kidmd/WDW-costumes/3d_panels/active_artwork.png

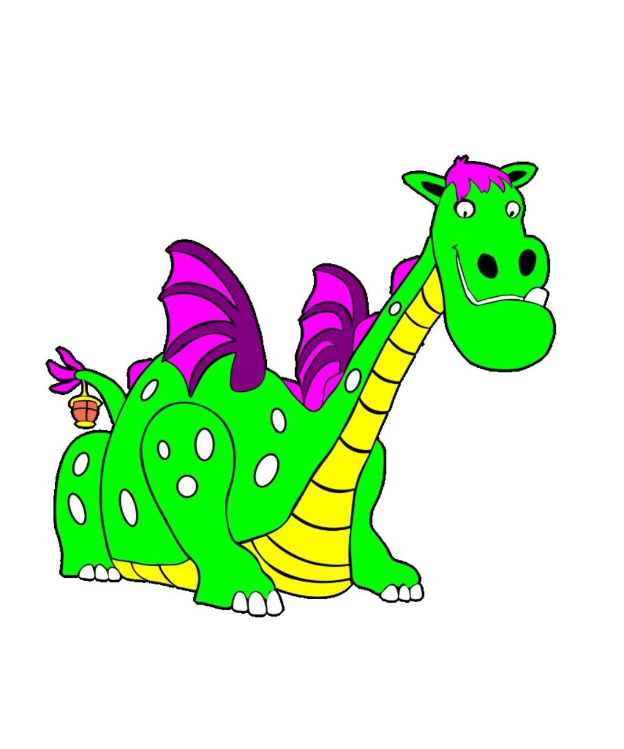
3d_panels/active_artwork.png
