kidmd/WDW-costumes/assets/petes_dragon.png

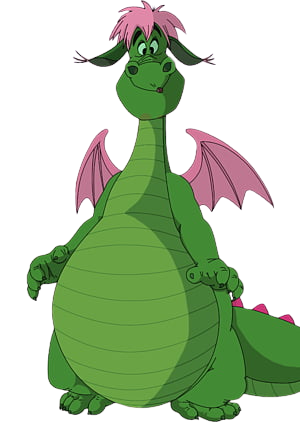
assets/petes_dragon.png
