kidmd/WDW-costumes/assets/snail2_raw_upload.png

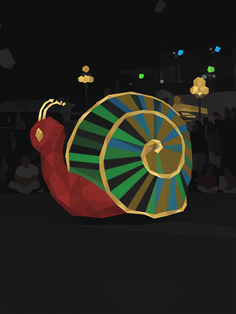
assets/snail2_raw_upload.png
