kidmd/WDW-costumes/assets/spinning_turtle.png

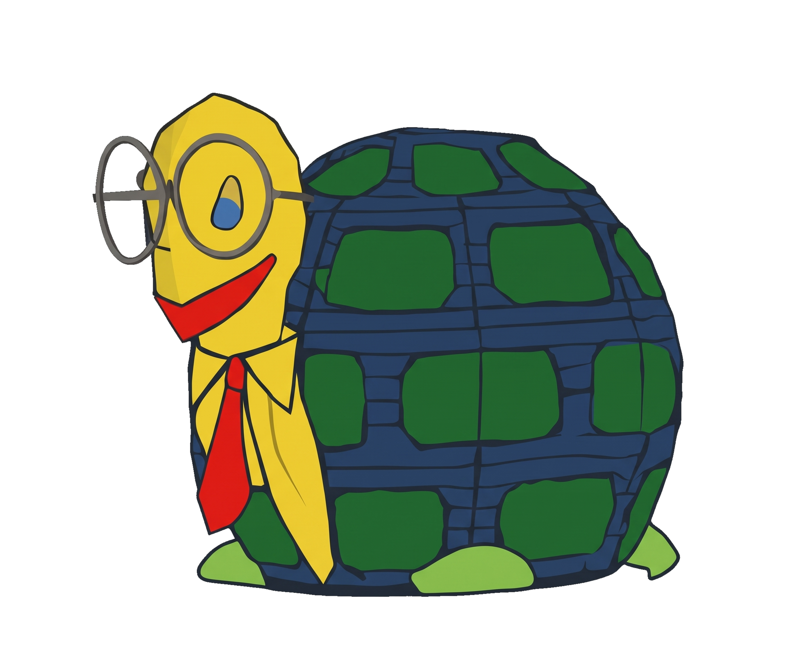
assets/spinning_turtle.png
