kidmd/WDW-costumes/assets/title_drum.png

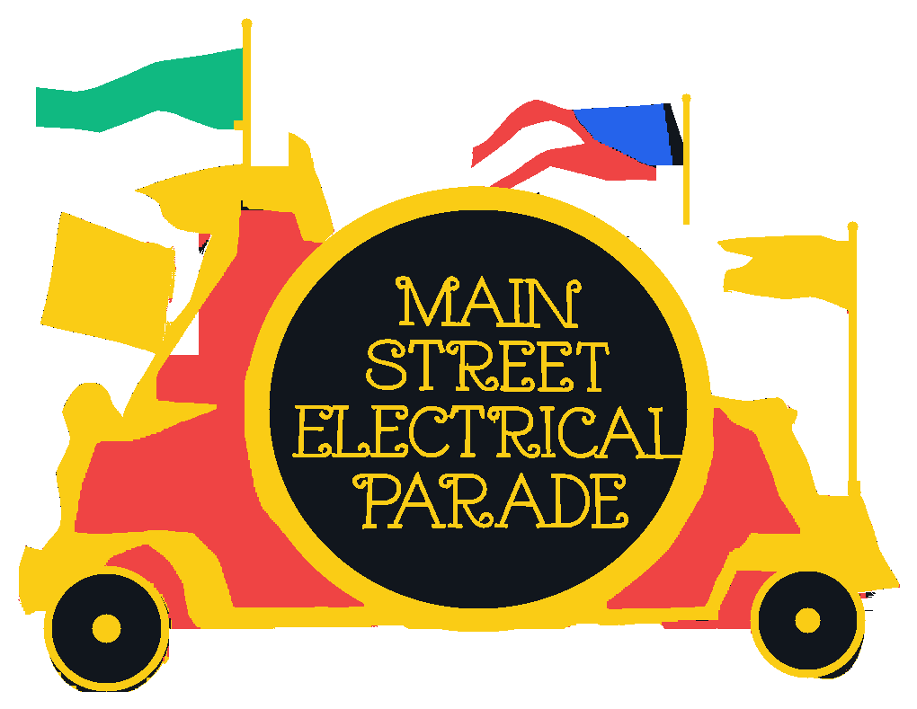
assets/title_drum.png
