kidmd/WDW-costumes/assets/Turtle_clean.jpg

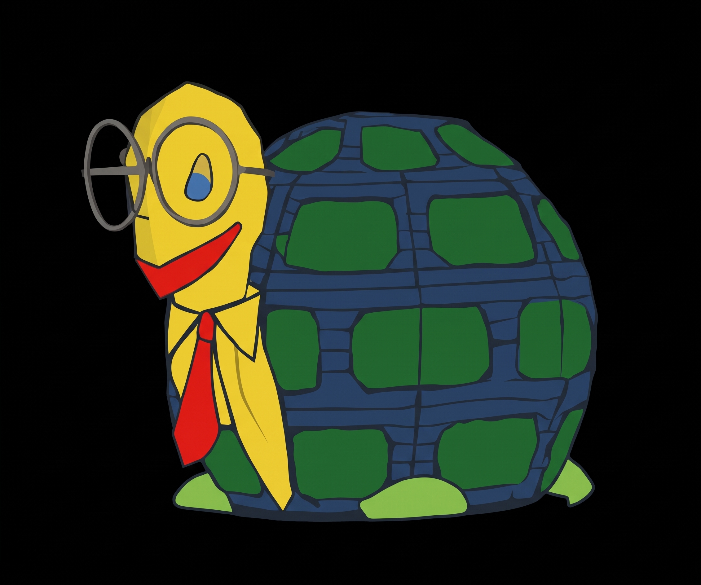
assets/Turtle_clean.jpg
