kidmd/WDW-costumes/simulator/assets/Snail.png

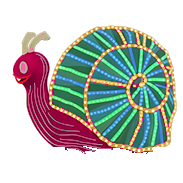
simulator/assets/Snail.png
