kidmd/WDW-costumes/simulator/assets/Turtle.png

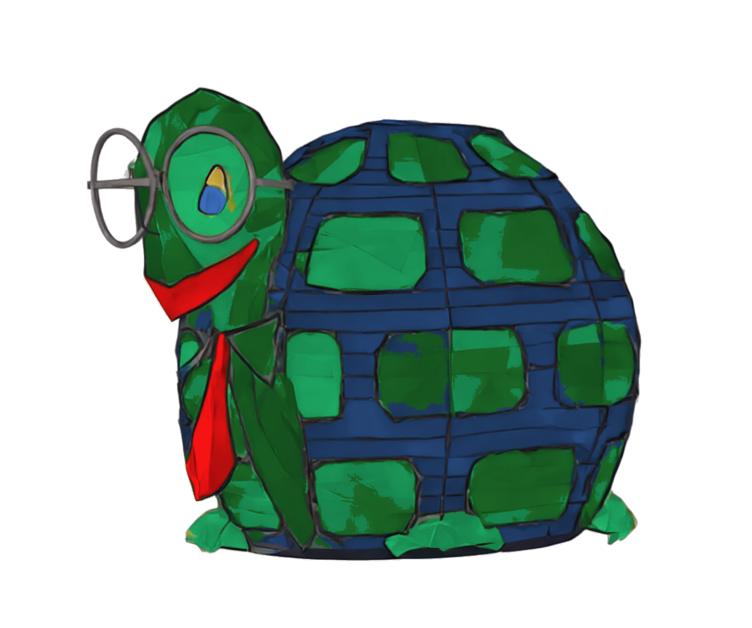
simulator/assets/Turtle.png
