kidmd/WDW-costumes/arduino/MSEP_Costume/fleet_palettes.h

#ifndef FLEET_PALETTES_H
#define FLEET_PALETTES_H

#include <FastLED.h>

#define HAS_DEFAULT_FLOAT_PALETTES 1

// Authentic default background graphic colors for all 7 floats (100 LEDs each)
// Used for 📸 Castle Photo Mode and default float palettes
const CRGB PROGMEM DEFAULT_FLOAT_PALETTES[7][100] = {
    // Float 1: The Train (Casey Jr.)
    {
        CRGB(255, 183, 3),
        CRGB(255, 183, 3),
        CRGB(255, 183, 3),
        CRGB(255, 183, 3),
        CRGB(255, 183, 3),
        CRGB(255, 183, 3),
        CRGB(255, 183, 3),
        CRGB(255, 183, 3),
        CRGB(255, 183, 3),
        CRGB(255, 183, 3),
        CRGB(255, 183, 3),
        CRGB(255, 183, 3),
        CRGB(255, 183, 3),
        CRGB(255, 183, 3),
        CRGB(255, 183, 3),
        CRGB(255, 183, 3),
        CRGB(255, 183, 3),
        CRGB(255, 183, 3),
        CRGB(255, 183, 3),
        CRGB(255, 183, 3),
        CRGB(255, 183, 3),
        CRGB(255, 183, 3),
        CRGB(255, 183, 3),
        CRGB(255, 183, 3),
        CRGB(255, 183, 3),
        CRGB(255, 183, 3),
        CRGB(255, 183, 3),
        CRGB(255, 183, 3),
        CRGB(230, 57, 70),
        CRGB(230, 57, 70),
        CRGB(230, 57, 70),
        CRGB(230, 57, 70),
        CRGB(230, 57, 70),
        CRGB(230, 57, 70),
        CRGB(230, 57, 70),
        CRGB(230, 57, 70),
        CRGB(230, 57, 70),
        CRGB(230, 57, 70),
        CRGB(230, 57, 70),
        CRGB(230, 57, 70),
        CRGB(230, 57, 70),
        CRGB(230, 57, 70),
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
        CRGB(40, 90, 240),
        CRGB(40, 90, 240),
        CRGB(40, 90, 240),
        CRGB(230, 40, 40),
        CRGB(230, 40, 40),
        CRGB(230, 40, 40),
        CRGB(230, 40, 40),
        CRGB(230, 40, 40),
        CRGB(230, 40, 40)
    }
};

#endif // FLEET_PALETTES_H
