kidmd/WDW-costumes/simulator.py

#!/usr/bin/env python3
"""
Main Street Electrical Parade - LED Costume Simulator & Visualizer
Serves the interactive web interface locally and manages costume preset files.
"""

import http.server
import socketserver
import os
import sys
import json
import webbrowser
import threading
import urllib.parse
import socket
import re
import subprocess
import time
import math

# UDP Pixel Streaming Socket
udp_socket = socket.socket(socket.AF_INET, socket.SOCK_DGRAM)
try:
    udp_socket.setsockopt(socket.SOL_SOCKET, socket.SO_BROADCAST, 1)
except Exception as e:
    print(f"[WARN] Could not enable SO_BROADCAST on UDP socket: {e}")
UDP_STREAM_PORT = 4210

DEFAULT_PORT = 8000
BASE_DIR = os.path.dirname(os.path.abspath(__file__))
SIMULATOR_DIR = os.path.join(BASE_DIR, "simulator")
PRESETS_DIR = os.path.join(BASE_DIR, "presets")
FLEET_SHOWS_DIR = os.path.join(PRESETS_DIR, "fleet_shows")

# Ensure presets and fleet_shows directories exist
os.makedirs(PRESETS_DIR, exist_ok=True)
os.makedirs(FLEET_SHOWS_DIR, exist_ok=True)

class SimulatorRequestHandler(http.server.SimpleHTTPRequestHandler):
    def __init__(self, *args, **kwargs):
        super().__init__(*args, directory=SIMULATOR_DIR, **kwargs)

    def log_message(self, format, *args):
        # Keep console output concise
        pass

    def end_headers(self):
        self.send_header("Cache-Control", "no-store, no-cache, must-revalidate, max-age=0")
        self.send_header("Pragma", "no-cache")
        self.send_header("Expires", "0")
        super().end_headers()

    def do_GET(self):
        parsed = urllib.parse.urlparse(self.path)
        if parsed.path == "/api/presets":
            self.handle_list_presets()
        elif parsed.path == "/api/serial_status":
            self.handle_serial_status()
        elif parsed.path == "/api/wifi_config":
            self.handle_get_wifi_config()
        elif parsed.path == "/api/fleet_config":
            self.handle_get_fleet_config()
        elif parsed.path == "/api/fleet_shows":
            self.handle_list_fleet_shows()
        elif parsed.path == "/api/fleet_radar":
            self.handle_get_fleet_radar()
        elif parsed.path == "/api/build_fleet_binaries":
            self.handle_build_fleet_binaries()
        elif parsed.path == "/api/generate_tpu_stl":
            self.handle_generate_tpu_stl()
        elif parsed.path.startswith("/api/fleet_show/"):
            filename = urllib.parse.unquote(parsed.path[len("/api/fleet_show/"):])
            self.handle_get_fleet_show(filename)
        elif parsed.path.startswith("/api/preset/"):
            filename = urllib.parse.unquote(parsed.path[len("/api/preset/"):])
            self.handle_get_preset(filename)
        elif parsed.path.startswith("/firmware/"):
            rel_path = parsed.path[len("/firmware/"):]
            firmware_file = os.path.join(BASE_DIR, "firmware", rel_path)
            if os.path.exists(firmware_file) and os.path.isfile(firmware_file):
                self.send_response(200)
                if firmware_file.endswith(".bin"):
                    self.send_header("Content-Type", "application/octet-stream")
                elif firmware_file.endswith(".json"):
                    self.send_header("Content-Type", "application/json")
                else:
                    self.send_header("Content-Type", "text/plain")
                self.send_header("Content-Length", str(os.path.getsize(firmware_file)))
                self.send_header("Access-Control-Allow-Origin", "*")
                self.end_headers()
                with open(firmware_file, "rb") as f:
                    self.wfile.write(f.read())
                return
            else:
                self.send_error(404, "Firmware file not found")
                return
        elif parsed.path == "/SIMULATOR_USER_GUIDE.md":
            guide_path = os.path.join(BASE_DIR, "SIMULATOR_USER_GUIDE.md")
            if os.path.exists(guide_path):
                self.send_response(200)
                self.send_header("Content-Type", "text/markdown; charset=utf-8")
                self.send_header("Content-Length", str(os.path.getsize(guide_path)))
                self.end_headers()
                with open(guide_path, "rb") as f:
                    self.wfile.write(f.read())
                return
            else:
                self.send_error(404, "Guide not found")
                return
        elif parsed.path.startswith("/assets/"):
            rel_asset = urllib.parse.unquote(parsed.path[len("/assets/"):])
            # Check simulator/assets first, then root assets
            asset_path = os.path.join(SIMULATOR_DIR, "assets", rel_asset)
            if not os.path.exists(asset_path):
                asset_path = os.path.join(BASE_DIR, "assets", rel_asset)
            if os.path.exists(asset_path) and os.path.isfile(asset_path):
                self.send_response(200)
                if asset_path.endswith(".png"):
                    self.send_header("Content-Type", "image/png")
                elif asset_path.endswith(".jpg") or asset_path.endswith(".jpeg"):
                    self.send_header("Content-Type", "image/jpeg")
                elif asset_path.endswith(".svg"):
                    self.send_header("Content-Type", "image/svg+xml")
                else:
                    self.send_header("Content-Type", "application/octet-stream")
                self.send_header("Content-Length", str(os.path.getsize(asset_path)))
                self.send_header("Access-Control-Allow-Origin", "*")
                self.end_headers()
                with open(asset_path, "rb") as f:
                    self.wfile.write(f.read())
                return
            else:
                self.send_error(404, "Asset file not found")
                return
        elif parsed.path.startswith("/pcb/"):
            rel_pcb = urllib.parse.unquote(parsed.path[len("/pcb/"):])
            if not rel_pcb or rel_pcb == "/":
                rel_pcb = "pcb_preview.html"
            pcb_file = os.path.join(BASE_DIR, "pcb", rel_pcb)
            if os.path.exists(pcb_file) and os.path.isfile(pcb_file):
                self.send_response(200)
                if pcb_file.endswith(".html"):
                    self.send_header("Content-Type", "text/html; charset=utf-8")
                elif pcb_file.endswith(".csv"):
                    self.send_header("Content-Type", "text/csv; charset=utf-8")
                elif pcb_file.endswith(".kicad_pcb"):
                    self.send_header("Content-Type", "text/plain; charset=utf-8")
                else:
                    self.send_header("Content-Type", "application/octet-stream")
                self.send_header("Content-Length", str(os.path.getsize(pcb_file)))
                self.send_header("Access-Control-Allow-Origin", "*")
                self.end_headers()
                with open(pcb_file, "rb") as f:
                    self.wfile.write(f.read())
                return
            else:
                self.send_error(404, "PCB file not found")
                return
        elif parsed.path.startswith("/3d_panels/"):
            rel_panel = urllib.parse.unquote(parsed.path[len("/3d_panels/"):])
            if not rel_panel or rel_panel == "/":
                rel_panel = "tpu_panel_preview.html"
            panel_file = os.path.join(BASE_DIR, "3d_panels", rel_panel)
            if os.path.exists(panel_file) and os.path.isfile(panel_file):
                self.send_response(200)
                if panel_file.endswith(".html"):
                    self.send_header("Content-Type", "text/html; charset=utf-8")
                elif panel_file.endswith(".json"):
                    self.send_header("Content-Type", "application/json; charset=utf-8")
                elif panel_file.endswith(".3mf"):
                    self.send_header("Content-Type", "model/3mf")
                elif panel_file.endswith(".zip"):
                    self.send_header("Content-Type", "application/zip")
                elif panel_file.endswith(".stl"):
                    self.send_header("Content-Type", "model/stl")
                elif panel_file.endswith(".scad"):
                    self.send_header("Content-Type", "application/octet-stream")
                else:
                    self.send_header("Content-Type", "application/octet-stream")
                self.send_header("Content-Length", str(os.path.getsize(panel_file)))
                self.send_header("Access-Control-Allow-Origin", "*")
                self.send_header("Cache-Control", "no-cache, no-store, must-revalidate")
                self.send_header("Pragma", "no-cache")
                self.send_header("Expires", "0")
                self.end_headers()
                with open(panel_file, "rb") as f:
                    self.wfile.write(f.read())
                return
            else:
                self.send_error(404, "3D Panel file not found")
                return
        else:
            super().do_GET()

    def do_POST(self):
        parsed = urllib.parse.urlparse(self.path)
        if parsed.path == "/api/save_preset":
            self.handle_save_preset()
        elif parsed.path == "/api/save_fleet_config":
            self.handle_save_fleet_config()
        elif parsed.path == "/api/save_fleet_show":
            self.handle_save_fleet_show()
        elif parsed.path == "/api/flash_firmware":
            self.handle_flash_firmware()
        elif parsed.path == "/api/stream_pixels":
            self.handle_stream_pixels()
        elif parsed.path == "/api/save_wifi":
            self.handle_save_wifi()
        elif parsed.path == "/api/flash_wifi_receiver":
            self.handle_flash_wifi_receiver()
        elif parsed.path == "/api/export_fleet_routine":
            self.handle_export_fleet_routine()
        elif parsed.path == "/api/build_fleet_binaries":
            self.handle_build_fleet_binaries()
        elif parsed.path == "/api/fleet_radar/scan":
            self.handle_fleet_radar_scan()
        elif parsed.path == "/api/fleet_radar/identify":
            self.handle_fleet_radar_identify()
        elif parsed.path == "/api/fleet_radar/trigger_roll_call":
            self.handle_fleet_radar_trigger_roll_call()
        elif parsed.path == "/api/generate_tpu_stl":
            self.handle_generate_tpu_stl()
        else:
            self.send_error(404, "Endpoint not found")

    def handle_list_presets(self):
        try:
            ignore_files = {"fleet_lineup.json", "wifi_settings.json", "wifi_settings.example.json"}
            files = [f for f in sorted(os.listdir(PRESETS_DIR)) if f.endswith(".json") and f not in ignore_files and os.path.isfile(os.path.join(PRESETS_DIR, f))]
            presets = []
            for f in files:
                filepath = os.path.join(PRESETS_DIR, f)
                try:
                    with open(filepath, "r", encoding="utf-8") as pf:
                        data = json.load(pf)
                        presets.append({
                            "filename": f,
                            "name": data.get("name", f.replace(".json", "")),
                            "floatName": data.get("floatName", "Custom Float"),
                            "ledCount": len(data.get("leds", []))
                        })
                except Exception:
                    presets.append({"filename": f, "name": f.replace(".json", "")})

            self.send_response(200)
            self.send_header("Content-Type", "application/json")
            self.end_headers()
            self.wfile.write(json.dumps(presets).encode("utf-8"))
        except Exception as e:
            self.send_error(500, str(e))

    def handle_get_preset(self, filename):
        safe_name = os.path.basename(filename)
        filepath = os.path.join(PRESETS_DIR, safe_name)
        if not os.path.exists(filepath):
            self.send_error(404, "Preset not found")
            return
        try:
            with open(filepath, "r", encoding="utf-8") as f:
                content = f.read()
            self.send_response(200)
            self.send_header("Content-Type", "application/json")
            self.end_headers()
            self.wfile.write(content.encode("utf-8"))
        except Exception as e:
            self.send_error(500, str(e))

    def handle_save_preset(self):
        try:
            content_length = int(self.headers.get("Content-Length", 0))
            post_data = self.rfile.read(content_length)
            preset_data = json.loads(post_data.decode("utf-8"))
            
            raw_name = preset_data.get("name", "untitled_preset")
            allow_overwrite = preset_data.get("overwrite", False)

            # Sanitize filename
            safe_name = "".join(c for c in raw_name if c.isalnum() or c in (' ', '_', '-')).rstrip()
            safe_name = safe_name.replace(" ", "_").lower() + ".json"
            
            filepath = os.path.join(PRESETS_DIR, safe_name)
            if os.path.exists(filepath) and not allow_overwrite:
                # Return conflict 409 with duplicate info
                self.send_response(409)
                self.send_header("Content-Type", "application/json")
                self.end_headers()
                self.wfile.write(json.dumps({
                    "conflict": True,
                    "filename": safe_name,
                    "message": f"A preset file named '{safe_name}' already exists."
                }).encode("utf-8"))
                return

            with open(filepath, "w", encoding="utf-8") as f:
                json.dump(preset_data, f, indent=2)

            self.send_response(200)
            self.send_header("Content-Type", "application/json")
            self.end_headers()
            self.wfile.write(json.dumps({"success": True, "filename": safe_name}).encode("utf-8"))
        except Exception as e:
            self.send_error(500, str(e))

    def handle_get_fleet_config(self):
        filepath = os.path.join(PRESETS_DIR, "fleet_lineup.json")
        if os.path.exists(filepath):
            try:
                with open(filepath, "r", encoding="utf-8") as f:
                    content = f.read()
                self.send_response(200)
                self.send_header("Content-Type", "application/json")
                self.end_headers()
                self.wfile.write(content.encode("utf-8"))
                return
            except Exception as e:
                pass
        # Default lineup fallback
        default_fleet = [
            {"slot": 0, "bib": "01", "name": "The Train", "tag": "CASEY JR.", "color": "#e63946", "preset": "server:casey_jr_train.json"},
            {"slot": 1, "bib": "02", "name": "Title Drum", "tag": "THE DRUM", "color": "#ffb703", "preset": "server:title_drum.json"},
            {"slot": 2, "bib": "03", "name": "The Turtle", "tag": "TURTLE", "color": "#2ec4b6", "preset": "server:spinning_turtle.json"},
            {"slot": 3, "bib": "04", "name": "The Snail", "tag": "SNAIL", "color": "#ff007f", "preset": "server:spinning_snail.json"},
            {"slot": 4, "bib": "05", "name": "Cinderella", "tag": "COACH", "color": "#48cae4", "preset": "server:cinderellas_coach.json"},
            {"slot": 5, "bib": "06", "name": "Pete's Dragon", "tag": "ELLIOTT", "color": "#00ff88", "preset": "server:petes_dragon.json"},
            {"slot": 6, "bib": "07", "name": "Flag & Eagle", "tag": "HONOR AMERICA", "color": "#3a86ff", "preset": "server:honor_america_eagle.json"}
        ]
        self.send_response(200)
        self.send_header("Content-Type", "application/json")
        self.end_headers()
        self.wfile.write(json.dumps(default_fleet, indent=2).encode("utf-8"))

    def handle_save_fleet_config(self):
        try:
            content_length = int(self.headers.get("Content-Length", 0))
            post_data = self.rfile.read(content_length)
            payload = json.loads(post_data.decode("utf-8"))

            fleet_lineup = payload.get("lineup", payload) if isinstance(payload, dict) else payload
            allow_overwrite = payload.get("overwrite", False) if isinstance(payload, dict) else False
            fleet_name = payload.get("name", None) if isinstance(payload, dict) else None

            # 1. If a named fleet save was requested, check duplicate conflict & save to presets/
            saved_named_filename = None
            if fleet_name:
                raw_name = fleet_name.strip()
                safe_name = "".join(c for c in raw_name if c.isalnum() or c in (' ', '_', '-')).rstrip()
                safe_name = safe_name.replace(" ", "_").lower()
                if not safe_name.startswith("parade_fleet") and "fleet" not in safe_name:
                    safe_name = f"parade_fleet_{safe_name}"
                if not safe_name.endswith(".json"):
                    safe_name += ".json"

                named_filepath = os.path.join(PRESETS_DIR, safe_name)
                if os.path.exists(named_filepath) and not allow_overwrite:
                    self.send_response(409)
                    self.send_header("Content-Type", "application/json")
                    self.end_headers()
                    self.wfile.write(json.dumps({
                        "conflict": True,
                        "filename": safe_name,
                        "message": f"A parade fleet file named '{safe_name}' already exists."
                    }).encode("utf-8"))
                    return

                with open(named_filepath, "w", encoding="utf-8") as nf:
                    json.dump(payload if isinstance(payload, dict) else {"name": fleet_name, "lineup": fleet_lineup}, nf, indent=2)
                saved_named_filename = safe_name

            # 2. Always persist current lineup to presets/fleet_lineup.json for active simulator startup
            active_filepath = os.path.join(PRESETS_DIR, "fleet_lineup.json")
            with open(active_filepath, "w", encoding="utf-8") as f:
                json.dump(fleet_lineup, f, indent=2)

            self.send_response(200)
            self.send_header("Content-Type", "application/json")
            self.end_headers()
            self.wfile.write(json.dumps({
                "success": True,
                "filename": saved_named_filename or "fleet_lineup.json"
            }).encode("utf-8"))
        except Exception as e:
            self.send_error(500, str(e))

    def handle_list_fleet_shows(self):
        try:
            files = [f for f in os.listdir(FLEET_SHOWS_DIR) if f.endswith(".json")]
            shows = []
            for f in files:
                filepath = os.path.join(FLEET_SHOWS_DIR, f)
                try:
                    with open(filepath, "r", encoding="utf-8") as pf:
                        data = json.load(pf)
                        shows.append({
                            "filename": f,
                            "id": data.get("id", f.replace(".json", "")),
                            "name": data.get("name", f.replace(".json", "")),
                            "description": data.get("description", ""),
                            "loopDuration": data.get("loopDuration", 30.0),
                            "blockCount": len(data.get("blocks", []))
                        })
                except Exception:
                    shows.append({"filename": f, "name": f.replace(".json", "")})

            self.send_response(200)
            self.send_header("Content-Type", "application/json")
            self.end_headers()
            self.wfile.write(json.dumps(shows, indent=2).encode("utf-8"))
        except Exception as e:
            self.send_error(500, str(e))

    def handle_get_fleet_show(self, filename):
        safe_name = os.path.basename(filename)
        filepath = os.path.join(FLEET_SHOWS_DIR, safe_name)
        if not os.path.exists(filepath):
            self.send_error(404, "Fleet show not found")
            return
        try:
            with open(filepath, "r", encoding="utf-8") as f:
                content = f.read()
            self.send_response(200)
            self.send_header("Content-Type", "application/json")
            self.end_headers()
            self.wfile.write(content.encode("utf-8"))
        except Exception as e:
            self.send_error(500, str(e))

    def handle_save_fleet_show(self):
        try:
            content_length = int(self.headers.get("Content-Length", 0))
            post_data = self.rfile.read(content_length)
            show_data = json.loads(post_data.decode("utf-8"))

            raw_name = show_data.get("name", show_data.get("id", "untitled_fleet_show"))
            allow_overwrite = show_data.get("overwrite", False)
            safe_name = "".join(c for c in raw_name if c.isalnum() or c in (' ', '_', '-')).rstrip()
            safe_name = safe_name.replace(" ", "_").lower() + ".json"

            filepath = os.path.join(FLEET_SHOWS_DIR, safe_name)
            if os.path.exists(filepath) and not allow_overwrite:
                self.send_response(409)
                self.send_header("Content-Type", "application/json")
                self.end_headers()
                self.wfile.write(json.dumps({
                    "conflict": True,
                    "filename": safe_name,
                    "message": f"A fleet show routine file named '{safe_name}' already exists."
                }).encode("utf-8"))
                return

            with open(filepath, "w", encoding="utf-8") as f:
                json.dump(show_data, f, indent=2)

            self.send_response(200)
            self.send_header("Content-Type", "application/json")
            self.end_headers()
            self.wfile.write(json.dumps({"success": True, "filename": safe_name}).encode("utf-8"))
        except Exception as e:
            self.send_error(500, str(e))

    def handle_export_fleet_routine(self):
        try:
            content_length = int(self.headers.get("Content-Length", 0))
            post_data = self.rfile.read(content_length)
            payload = json.loads(post_data.decode("utf-8"))

            cpp_code = payload.get("cppCode", "").strip()
            loop_duration = float(payload.get("loopDuration", 30.0))
            total_ms = int(round(loop_duration * 1000))
            show_name = payload.get("showName", "Custom Fleet Show")
            verify_compile = bool(payload.get("verifyCompile", True))

            if not cpp_code:
                self.send_error(400, "Missing cppCode payload")
                return

            main_cpp_path = os.path.join(BASE_DIR, "src", "main.cpp")
            ino_path = os.path.join(BASE_DIR, "arduino", "MSEP_Costume", "MSEP_Costume.ino")

            begin_sentinel = "// >>>>> BEGIN AUTO-GENERATED FLEET ROUTINE >>>>>"
            end_sentinel = "// <<<<< END AUTO-GENERATED FLEET ROUTINE <<<<<"

            def update_file(file_path):
                if not os.path.exists(file_path):
                    return False, f"File not found: {file_path}"
                with open(file_path, "r", encoding="utf-8") as f:
                    content = f.read()

                # 1. Update FLEET_ROUTINE_TOTAL_MS define
                pattern_define = r"#define\s+FLEET_ROUTINE_TOTAL_MS\s+\d+[^\n]*"
                new_define = f"#define FLEET_ROUTINE_TOTAL_MS {total_ms} // Auto-updated for {show_name} ({loop_duration:.1f}s)"
                if re.search(pattern_define, content):
                    content = re.sub(pattern_define, new_define, content)
                else:
                    pattern_show = r"(#define\s+SHOW_LOOP_MS\s+\d+[^\n]*\n)"
                    content = re.sub(pattern_show, r"\1" + new_define + "\n", content)

                # 2. Replace render30sFleetRoutine between sentinels
                if begin_sentinel in content and end_sentinel in content:
                    parts = content.split(begin_sentinel, 1)
                    before = parts[0]
                    after = parts[1].split(end_sentinel, 1)[1]
                    content = before + begin_sentinel + "\n" + cpp_code + "\n" + end_sentinel + after
                else:
                    return False, f"Sentinels missing in {file_path}"

                with open(file_path, "w", encoding="utf-8") as f:
                    f.write(content)
                return True, "OK"

            ok_main, err_main = update_file(main_cpp_path)
            ok_ino, err_ino = update_file(ino_path)

            if not ok_main or not ok_ino:
                self.send_response(500)
                self.send_header("Content-Type", "application/json")
                self.end_headers()
                self.wfile.write(json.dumps({
                    "success": False,
                    "error": f"Failed updating files: main.cpp ({err_main}), MSEP_Costume.ino ({err_ino})"
                }).encode("utf-8"))
                return

            compile_result = {"tested": False, "success": True, "output": ""}
            if verify_compile:
                try:
                    cmd = [sys.executable, "-m", "platformio", "run"]
                    res = subprocess.run(
                        cmd,
                        cwd=BASE_DIR,
                        capture_output=True,
                        text=True,
                        timeout=60
                    )
                    compile_result["tested"] = True
                    compile_result["success"] = (res.returncode == 0)
                    compile_result["output"] = res.stdout[-600:] if res.stdout else res.stderr[-600:]
                    if compile_result["success"]:
                        try:
                            pio_fw = os.path.join(BASE_DIR, ".pio", "build", "esp32dev", "firmware.bin")
                            firmware_dir = os.path.join(BASE_DIR, "firmware")
                            if os.path.exists(pio_fw):
                                shutil.copy2(pio_fw, os.path.join(firmware_dir, "firmware.bin"))
                            # Rebuild all 7 float binaries in background to sync Web Flasher
                            subprocess.Popen([sys.executable, "build_fleet_binaries.py"], cwd=BASE_DIR, stdout=subprocess.DEVNULL, stderr=subprocess.DEVNULL)
                        except Exception as fe:
                            print(f"[WARN] Failed auto-syncing firmware binaries: {fe}")
                except Exception as ce:
                    compile_result["tested"] = True
                    compile_result["success"] = False
                    compile_result["output"] = str(ce)

            self.send_response(200)
            self.send_header("Content-Type", "application/json")
            self.end_headers()
            self.wfile.write(json.dumps({
                "success": True,
                "totalMs": total_ms,
                "loopDuration": loop_duration,
                "showName": show_name,
                "compileResult": compile_result
            }).encode("utf-8"))

        except Exception as e:
            self.send_error(500, str(e))

    def handle_serial_status(self):
        try:
            port = get_connected_esp32_port()
            all_ports = []
            try:
                import serial.tools.list_ports
                all_ports = [{"device": p.device, "description": p.description} for p in serial.tools.list_ports.comports()]
            except Exception:
                pass

            ready = False
            error_msg = None
            if port:
                try:
                    import serial
                    s = serial.Serial(port, 115200, timeout=0.1)
                    s.close()
                    ready = True
                except Exception as ex:
                    ready = False
                    error_msg = str(ex)

            self.send_response(200)
            self.send_header("Content-Type", "application/json")
            self.end_headers()
            self.wfile.write(json.dumps({
                "connected": bool(port),
                "ready": ready,
                "port": port,
                "error": error_msg,
                "all_ports": all_ports
            }).encode("utf-8"))
        except Exception as e:
            self.send_error(500, str(e))

    def handle_flash_firmware(self):
        try:
            content_length = int(self.headers.get("Content-Length", 0))
            post_data = self.rfile.read(content_length)
            payload = json.loads(post_data.decode("utf-8"))
            
            num_front = int(payload.get("numLeds", 100))
            num_back = num_front
            total_leds = num_front + num_back  # 200 LEDs (100 front + 100 back duplicated)
            pattern_str = payload.get("pattern", "steady_sparkle")
            ambient_pattern_str = payload.get("ambientPattern", "steady_sparkle")
            ambient_dir = int(payload.get("ambientDirection", 1))
            sparkle_style = payload.get("sparkleStyle", "incandescent")
            ambient_color_mode = payload.get("ambientColorMode", "artwork")
            ambient_custom_hex = str(payload.get("ambientCustomColor", "#ffb703")).lstrip("#")
            
            sparkle_style_map = {"incandescent": 0, "diamond": 1, "gold": 2}
            sparkle_style_code = sparkle_style_map.get(sparkle_style, 0)
            
            color_mode_map = {"artwork": 0, "float_theme": 1, "vintage_warm": 2, "custom": 3}
            color_mode_code = color_mode_map.get(ambient_color_mode, 0)
            
            try:
                c_r = int(ambient_custom_hex[0:2], 16)
                c_g = int(ambient_custom_hex[2:4], 16)
                c_b = int(ambient_custom_hex[4:6], 16)
            except Exception:
                c_r, c_g, c_b = 255, 183, 3

            speed_bpm = int(payload.get("speedBpm", 120))
            sparkle_rate = float(payload.get("sparkleRate", 1.5))
            green_hue = int(payload.get("greenHue", 140))
            brightness_pct = int(payload.get("brightness", 80))
            fastled_brightness = max(30, min(85, int(brightness_pct * 85 / 100)))
            palette = payload.get("palette", [])
            
            pattern_map = {
                "steady_sparkle": "COSTUME_PATTERN_STEADY_SPARKLE",
                "color_match": "COSTUME_PATTERN_BREATHING_GLOW",
                "dragon_sparkle": "COSTUME_PATTERN_STEADY_SPARKLE",
                "breathing_glow": "COSTUME_PATTERN_BREATHING_GLOW",
                "fire_breath": "COSTUME_PATTERN_FIRE_BREATH",
                "traveling_wave": "COSTUME_PATTERN_TRAVELING_WAVE",
                "marquee": "COSTUME_PATTERN_MARQUEE",
                "photo_mode": "COSTUME_PATTERN_PHOTO_MODE",
                "fireworks": "COSTUME_PATTERN_FIREWORKS",
                "comet": "COSTUME_PATTERN_COMET",
                "scanner": "COSTUME_PATTERN_SCANNER",
                "color_wipe": "COSTUME_PATTERN_COLOR_WIPE",
                "write_on_off": "COSTUME_PATTERN_COLOR_WIPE",
                "pixie_dust": "COSTUME_PATTERN_PIXIE_DUST",
                "filament_glow": "COSTUME_PATTERN_FILAMENT_GLOW",
                "candle_flicker": "COSTUME_PATTERN_CANDLE_FLICKER",
                "tidal_ripple": "COSTUME_PATTERN_TIDAL_RIPPLE",
                "piston_chug": "COSTUME_PATTERN_PISTON_CHUG",
                "rainbow_cycle": "COSTUME_PATTERN_RAINBOW_CYCLE",
                "autonomous_90s": "COSTUME_PATTERN_AUTONOMOUS_90S",
                "off": "COSTUME_PATTERN_OFF",
                "flashlight": "COSTUME_PATTERN_FLASHLIGHT",
                "mouse_scamper": "COSTUME_PATTERN_MOUSE_SCAMPER"
            }
            active_pattern = pattern_map.get(pattern_str, "COSTUME_PATTERN_STEADY_SPARKLE")

            # Ambient fallback pattern: numeric code baked into AMBIENT_FALLBACK_PATTERN define
            # Matches the pattern constants: 0=steady_sparkle, 1=breathing_glow, 5=photo_mode, etc.
            ambient_pattern_numeric_map = {
                "steady_sparkle": 0,
                "color_match": 1,
                "dragon_sparkle": 0,
                "breathing_glow": 1,
                "fire_breath": 2,
                "traveling_wave": 3,
                "marquee": 4,
                "photo_mode": 5,
                "fireworks": 7,
                "comet": 8,
                "scanner": 9,
                "color_wipe": 10,
                "write_on_off": 10,
                "pixie_dust": 11,
                "filament_glow": 12,
                "candle_flicker": 13,
                "tidal_ripple": 14,
                "piston_chug": 15,
                "rainbow_cycle": 16,
                "off": 17,
                "flashlight": 18,
                "mouse_scamper": 19,
                "autonomous_90s": 0
            }
            ambient_fallback_code = ambient_pattern_numeric_map.get(ambient_pattern_str, 0)
            
            palette_lines = []
            # 1. Front LEDs (0 to num_front - 1)
            for i in range(num_front):
                if i < len(palette) and palette[i]:
                    c = palette[i]
                    r = int(c.get("r", 15))
                    g = int(c.get("g", 255))
                    b = int(c.get("b", 35))
                else:
                    r, g, b = (15, 255, 35)
                palette_lines.append(f"    CRGB({r}, {g}, {b}), // Front LED {i}")

            # 2. Back LEDs (num_front to total_leds - 1, duplicate of front)
            for i in range(num_back):
                if i < len(palette) and palette[i]:
                    c = palette[i]
                    r = int(c.get("r", 15))
                    g = int(c.get("g", 255))
                    b = int(c.get("b", 35))
                else:
                    r, g, b = (15, 255, 35)
                comma = "," if i < num_back - 1 else ""
                palette_lines.append(f"    CRGB({r}, {g}, {b}){comma} // Back LED {num_front + i} (Duplicate of {i})")
            
            sequence_cues = payload.get("sequenceCues", [])
            seq_loop_duration = float(payload.get("sequenceLoopDuration", 90.0))
            show_loop_ms = max(10000, int(seq_loop_duration * 1000))

            cue_effect_map = {
                "steady_sparkle": 0,
                "breathe": 1,
                "breathing_glow": 1,
                "color_match": 1,      # Color-Matched Breathing Glow
                "pulse": 1,            # Breathing Glow Pulse
                "pulse_slow": 1,       # Slow breathing
                "fire_breath": 2,
                "traveling_wave": 3,
                "marquee": 4,
                "chase": 8,            # chase maps to comet/chase
                "photo_mode": 5,       # Solid lit, no sparkle
                "off": 17,             # All Off / Completely Dark
                "fireworks": 6,
                "flash_slow": 7,       # Slow blink / flash
                "sparkle_storm": 8,    # High-density sparkle burst
                "write_on_off": 10,    # Theatrical write-on
                "color_wipe": 10,
                "rainbow_cycle": 16,   # Rainbow wave
                "comet": 8,
                "scanner": 9,
                "pixie_dust": 11,
                "filament_glow": 12,
                "candle_flicker": 13,
                "tidal_ripple": 14,
                "piston_chug": 15
            }

            cue_lines = []
            for q in sequence_cues:
                start_ms = int(float(q.get("startTime", 0)) * 1000)
                dur_ms = int(float(q.get("duration", 10)) * 1000)
                end_ms = start_ms + dur_ms
                eff_str = q.get("effect", "steady_sparkle")
                eff_code = cue_effect_map.get(eff_str, 0)
                bpm = int(q.get("speedBpm", 120))
                cue_lines.append(f"    {{ {start_ms}, {end_ms}, {eff_code}, {bpm} }}")

            has_cues = 1 if len(cue_lines) > 0 else 0
            cue_count = len(cue_lines)
            if cue_count == 0:
                cues_code = "    { 0, 0, 0, 0 } // No cues on timeline: pure ambient programming fallback"
                cue_count = 1
                has_cues = 0
            else:
                cues_code = ",\n".join(cue_lines)
            
            palette_code = "\n".join(palette_lines)

            # 2D Spatial Metrics Generation (X, Y, Bottom-Up Rank, and Centroid Radius)
            coords = payload.get("coords", [])
            led_pts = []
            for i in range(num_front):
                if i < len(coords) and isinstance(coords[i], dict):
                    px = float(coords[i].get("x", 0.5))
                    py = float(coords[i].get("y", 0.5))
                else:
                    px, py = 0.5, float(i) / max(1, num_front - 1)
                led_pts.append((px, py))

            min_x = min(p[0] for p in led_pts) if led_pts else 0.0
            max_x = max(p[0] for p in led_pts) if led_pts else 1.0
            min_y = min(p[1] for p in led_pts) if led_pts else 0.0
            max_y = max(p[1] for p in led_pts) if led_pts else 1.0
            cx = sum(p[0] for p in led_pts) / max(1, len(led_pts))
            cy = sum(p[1] for p in led_pts) / max(1, len(led_pts))
            span_x = max(0.001, max_x - min_x)
            span_y = max(0.001, max_y - min_y)

            radii = [math.hypot(p[0] - cx, p[1] - cy) for p in led_pts]
            max_r = max(radii) if radii and max(radii) > 0.001 else 1.0

            # Rank Y descending (bottom-up: highest y on shirt is rank 0, lowest y is num_front - 1)
            y_indices = list(range(num_front))
            y_indices.sort(key=lambda idx: (-led_pts[idx][1], led_pts[idx][0]))
            rank_y_bottom_up = [0] * num_front
            for rank, idx in enumerate(y_indices):
                rank_y_bottom_up[idx] = rank

            spatial_rank_y_lines = [f"    {rank_y_bottom_up[i]}" + ("," if i < num_front - 1 else "") + f" // Front LED {i}" for i in range(num_front)]
            spatial_x_lines = [f"    {int(max(0, min(255, (led_pts[i][0] - min_x) / span_x * 255)))}" + ("," if i < num_front - 1 else "") + f" // Front LED {i}" for i in range(num_front)]
            spatial_y_lines = [f"    {int(max(0, min(255, (led_pts[i][1] - min_y) / span_y * 255)))}" + ("," if i < num_front - 1 else "") + f" // Front LED {i}" for i in range(num_front)]
            spatial_radius_lines = [f"    {int(max(0, min(255, radii[i] / max_r * 255)))}" + ("," if i < num_front - 1 else "") + f" // Front LED {i}" for i in range(num_front)]

            spatial_rank_y_code = "\n".join(spatial_rank_y_lines)
            spatial_x_code = "\n".join(spatial_x_lines)
            spatial_y_code = "\n".join(spatial_y_lines)
            spatial_radius_code = "\n".join(spatial_radius_lines)
            
            header_content = f"""#ifndef COSTUME_CONFIG_H
#define COSTUME_CONFIG_H

#include <Arduino.h>
#include <FastLED.h>

// Automatically generated by MSEP Simulator (200 LEDs: 100 Front + 100 Back)
#define NUM_LEDS {total_leds}
#define FRONT_LEDS {num_front}
#define BACK_LEDS {num_back}
#define DUPLICATE_FRONT_TO_BACK 1

#define COSTUME_PATTERN_STEADY_SPARKLE   0
#define COSTUME_PATTERN_BREATHING_GLOW   1
#define COSTUME_PATTERN_FIRE_BREATH      2
#define COSTUME_PATTERN_TRAVELING_WAVE   3
#define COSTUME_PATTERN_MARQUEE          4
#define COSTUME_PATTERN_PHOTO_MODE       5
#define COSTUME_PATTERN_AUTONOMOUS_90S   6
#define COSTUME_PATTERN_FIREWORKS        7
#define COSTUME_PATTERN_COMET            8
#define COSTUME_PATTERN_SCANNER          9
#define COSTUME_PATTERN_COLOR_WIPE       10
#define COSTUME_PATTERN_PIXIE_DUST       11
#define COSTUME_PATTERN_FILAMENT_GLOW    12
#define COSTUME_PATTERN_CANDLE_FLICKER   13
#define COSTUME_PATTERN_TIDAL_RIPPLE     14
#define COSTUME_PATTERN_PISTON_CHUG      15
#define COSTUME_PATTERN_RAINBOW_CYCLE    16
#define COSTUME_PATTERN_OFF              17
#define COSTUME_PATTERN_FLASHLIGHT       18
#define COSTUME_PATTERN_MOUSE_SCAMPER    19

#define ACTIVE_COSTUME_PATTERN           {active_pattern}
#define COSTUME_SPEED_BPM                {speed_bpm}
#define COSTUME_SPARKLE_RATE             {sparkle_rate}
#define COSTUME_GREEN_HUE                {green_hue}
#define COSTUME_BRIGHTNESS               {fastled_brightness}
#define COLOR_ORDER                      RGB
#define HAS_CUSTOM_PALETTE               1
#define COSTUME_OVERRIDE_STANDALONE      1
#define AMBIENT_FALLBACK_PATTERN         {ambient_fallback_code}
#define COSTUME_AMBIENT_DIRECTION        {ambient_dir}
#define COSTUME_SPARKLE_STYLE            {sparkle_style_code}
#define COSTUME_AMBIENT_COLOR_MODE       {color_mode_code}
#define AMBIENT_CUSTOM_COLOR_RGB         CRGB({c_r}, {c_g}, {c_b})

#define SHOW_LOOP_MS                     {show_loop_ms}
#define HAS_CUSTOM_SEQUENCE_CUES         {has_cues}
#define CUSTOM_SEQUENCE_CUE_COUNT        {cue_count}
#define HAS_SPATIAL_METRICS              1

struct CostumeCue {{
    uint32_t startMs;
    uint32_t endMs;
    uint8_t effect;
    uint16_t speedBpm;
}};

const CostumeCue PROGMEM CUSTOM_SEQUENCE_CUES[{cue_count}] = {{
{cues_code}
}};

// Artwork Sampled Color Palette (PROGMEM Flash Storage)
const CRGB PROGMEM ARTWORK_PALETTE[NUM_LEDS] = {{
{palette_code}
}};

// 2D Spatial Metrics (PROGMEM Flash Storage)
// Allows 60 FPS spatial lighting sweeps without floating-point math
const uint8_t PROGMEM SPATIAL_RANK_Y[FRONT_LEDS] = {{
{spatial_rank_y_code}
}};

const uint8_t PROGMEM SPATIAL_X_BYTE[FRONT_LEDS] = {{
{spatial_x_code}
}};

const uint8_t PROGMEM SPATIAL_Y_BYTE[FRONT_LEDS] = {{
{spatial_y_code}
}};

const uint8_t PROGMEM SPATIAL_RADIUS_BYTE[FRONT_LEDS] = {{
{spatial_radius_code}
}};

#endif // COSTUME_CONFIG_H
"""
            include_dir = os.path.join(BASE_DIR, "include")
            os.makedirs(include_dir, exist_ok=True)
            config_path = os.path.join(include_dir, "costume_config.h")
            with open(config_path, "w", encoding="utf-8") as f:
                f.write(header_content)

            float_id = int(payload.get("floatId", 0))
            float_config_path = os.path.join(include_dir, "float_config.h")
            with open(float_config_path, "w", encoding="utf-8") as f:
                f.write(f"#ifndef FLOAT_CONFIG_H\n#define FLOAT_CONFIG_H\n\n#ifndef COMPILED_FLOAT_ID\n#define COMPILED_FLOAT_ID {float_id}\n#endif\n\n#endif // FLOAT_CONFIG_H\n")

            # Touch src/main.cpp to force PlatformIO to recompile with new header
            try:
                main_cpp_path = os.path.join(BASE_DIR, "src", "main.cpp")
                os.utime(main_cpp_path, None)
            except Exception:
                pass

            port = get_connected_esp32_port()
            if not port:
                self.send_response(200)
                self.send_header("Content-Type", "application/json")
                self.end_headers()
                self.wfile.write(json.dumps({
                    "success": False,
                    "error": "No ESP32 detected on USB serial ports. Please connect your ESP32 with a USB cable and try again."
                }).encode("utf-8"))
                return

            import subprocess
            cmd = [sys.executable, "-m", "platformio", "run", "-t", "upload", "--upload-port", port]
            proc = subprocess.Popen(
                cmd,
                cwd=BASE_DIR,
                stdout=subprocess.PIPE,
                stderr=subprocess.STDOUT,
                text=True
            )
            stdout, _ = proc.communicate(timeout=120)
            success = (proc.returncode == 0)
            user_error = None
            if success:
                try:
                    pio_fw = os.path.join(BASE_DIR, ".pio", "build", "esp32dev", "firmware.bin")
                    firmware_dir = os.path.join(BASE_DIR, "firmware")
                    if os.path.exists(pio_fw):
                        shutil.copy2(pio_fw, os.path.join(firmware_dir, "firmware.bin"))
                        if float_id > 0:
                            shutil.copy2(pio_fw, os.path.join(firmware_dir, f"firmware_float{float_id}.bin"))
                except Exception as cpy_err:
                    print(f"[WARN] Failed copying binary to firmware folder: {cpy_err}")
            else:
                if "not functioning" in stdout or "Error 31" in stdout or "PermissionError(13" in stdout:
                    user_error = f"USB Port {port} is unresponsive (Windows Error 31). Please UNPLUG the USB cable from the ESP32, wait 2 seconds, and plug it back in. Then click Flash again."
                elif "Wrong boot mode detected" in stdout or "needs to be in download mode" in stdout:
                    user_error = "ESP32 did not enter bootloader mode automatically. Hold down the BOOT button on your ESP32 board, click Flash again, and release BOOT once writing begins."
                elif "could not open port" in stdout or "PermissionError" in stdout or "Access is denied" in stdout:
                    user_error = f"Serial port {port} is busy or locked by another program (e.g. Serial Monitor). Close other apps using this COM port and try again."
                else:
                    user_error = f"PlatformIO upload failed with exit code {proc.returncode}"

            self.send_response(200)
            self.send_header("Content-Type", "application/json")
            self.end_headers()
            self.wfile.write(json.dumps({
                "success": success,
                "port": port,
                "floatId": float_id,
                "log": stdout,
                "error": user_error
            }).encode("utf-8"))
        except Exception as e:
            self.send_response(200)
            self.send_header("Content-Type", "application/json")
            self.end_headers()
            self.wfile.write(json.dumps({
                "success": False,
                "error": str(e)
            }).encode("utf-8"))

    def handle_stream_pixels(self):
        try:
            content_length = int(self.headers.get("Content-Length", 0))
            post_data = self.rfile.read(content_length)
            payload = json.loads(post_data.decode("utf-8"))
            target_ip = payload.get("targetIp", "255.255.255.255")
            if not target_ip or not target_ip.strip():
                target_ip = "255.255.255.255"

            # 1. Multi-Float Fleet Stream (Opcode 0x02 per float)
            fleet_frames = payload.get("fleetFrames")
            if fleet_frames and isinstance(fleet_frames, list):
                total_sent = 0
                total_bytes = 0
                for frame in fleet_frames:
                    float_id = int(frame.get("floatId", 0)) # 1-7 (or 0 for universal)
                    pixels = frame.get("pixels", [])
                    if pixels and isinstance(pixels[0], int):
                        # Fast Flat RGB Array: [r, g, b, r, g, b, ...]
                        num_leds = len(pixels) // 3
                        header = b'MSEP' + bytes([0x02, float_id & 0xFF]) + num_leds.to_bytes(2, 'big')
                        raw = bytearray(header)
                        for val in pixels:
                            raw.append(max(0, min(255, int(val))))
                    else:
                        num_leds = len(pixels)
                        header = b'MSEP' + bytes([0x02, float_id & 0xFF]) + num_leds.to_bytes(2, 'big')
                        raw = bytearray(header)
                        for p in pixels:
                            raw.append(max(0, min(255, int(p.get("r", 0)))))
                            raw.append(max(0, min(255, int(p.get("g", 0)))))
                            raw.append(max(0, min(255, int(p.get("b", 0)))))

                    udp_socket.sendto(bytes(raw), (target_ip, UDP_STREAM_PORT))
                    total_sent += 1
                    total_bytes += len(raw)

                self.send_response(200)
                self.send_header("Content-Type", "application/json")
                self.end_headers()
                self.wfile.write(json.dumps({
                    "success": True,
                    "mode": "fleet",
                    "framesSent": total_sent,
                    "totalBytes": total_bytes,
                    "targetIp": target_ip
                }).encode("utf-8"))
                return

            # 2. Single-Costume Stream (Opcode 0x01 universal, or Opcode 0x02 if floatId specified)
            pixels = payload.get("pixels", [])
            float_id = payload.get("floatId")
            if pixels and isinstance(pixels[0], int):
                # Fast Flat RGB Array
                num_leds = len(pixels) // 3
                if float_id is not None:
                    header = b'MSEP' + bytes([0x02, int(float_id) & 0xFF]) + num_leds.to_bytes(2, 'big')
                else:
                    header = b'MSEP' + bytes([0x01]) + num_leds.to_bytes(2, 'big')
                raw = bytearray(header)
                for val in pixels:
                    raw.append(max(0, min(255, int(val))))
            else:
                num_leds = len(pixels)
                if float_id is not None:
                    header = b'MSEP' + bytes([0x02, int(float_id) & 0xFF]) + num_leds.to_bytes(2, 'big')
                else:
                    header = b'MSEP' + bytes([0x01]) + num_leds.to_bytes(2, 'big')
                raw = bytearray(header)
                for p in pixels:
                    raw.append(max(0, min(255, int(p.get("r", 0)))))
                    raw.append(max(0, min(255, int(p.get("g", 0)))))
                    raw.append(max(0, min(255, int(p.get("b", 0)))))

            udp_socket.sendto(bytes(raw), (target_ip, UDP_STREAM_PORT))

            self.send_response(200)
            self.send_header("Content-Type", "application/json")
            self.end_headers()
            self.wfile.write(json.dumps({
                "success": True,
                "mode": "single",
                "count": num_leds,
                "bytes": len(raw),
                "targetIp": target_ip
            }).encode("utf-8"))
        except Exception as e:
            self.send_response(200)
            self.send_header("Content-Type", "application/json")
            self.end_headers()
            self.wfile.write(json.dumps({
                "success": False,
                "error": str(e)
            }).encode("utf-8"))

    def handle_get_wifi_config(self):
        try:
            wifi_file = os.path.join(PRESETS_DIR, "wifi_settings.json")
            config = {
                "ssid": "",
                "password": "",
                "targetIp": "255.255.255.255"
            }
            if os.path.exists(wifi_file):
                with open(wifi_file, "r", encoding="utf-8") as f:
                    config.update(json.load(f))
            self.send_response(200)
            self.send_header("Content-Type", "application/json")
            self.end_headers()
            self.wfile.write(json.dumps(config).encode("utf-8"))
        except Exception as e:
            self.send_error(500, str(e))

    def handle_save_wifi(self):
        try:
            content_length = int(self.headers.get("Content-Length", 0))
            post_data = self.rfile.read(content_length)
            payload = json.loads(post_data.decode("utf-8"))

            ssid = payload.get("ssid", "").strip()
            password = payload.get("password", "").strip()
            target_ip = payload.get("targetIp", "255.255.255.255").strip()

            wifi_file = os.path.join(PRESETS_DIR, "wifi_settings.json")
            with open(wifi_file, "w", encoding="utf-8") as f:
                json.dump({"ssid": ssid, "password": password, "targetIp": target_ip}, f, indent=2)

            header_content = f"""#ifndef WIFI_CONFIG_H
#define WIFI_CONFIG_H

#include <Arduino.h>

#define WIFI_SSID       "{ssid if ssid else 'YourWiFiNetwork'}"
#define WIFI_PASSWORD   "{password}"
#define UDP_STREAM_PORT 4210
#define AP_SSID         "MSEP-Costume-AP"
#define AP_PASSWORD     "msep1234"

#define MSEP_MAGIC_0    'M'
#define MSEP_MAGIC_1    'S'
#define MSEP_MAGIC_2    'E'
#define MSEP_MAGIC_3    'P'
#define MSEP_OPCODE_LIVE_FRAME  0x01
#define MSEP_OPCODE_FLEET_FRAME 0x02

#endif // WIFI_CONFIG_H
"""
            include_dir = os.path.join(BASE_DIR, "include")
            os.makedirs(include_dir, exist_ok=True)
            with open(os.path.join(include_dir, "wifi_config.h"), "w", encoding="utf-8") as f:
                f.write(header_content)

            self.send_response(200)
            self.send_header("Content-Type", "application/json")
            self.end_headers()
            self.wfile.write(json.dumps({"success": True}).encode("utf-8"))
        except Exception as e:
            self.send_response(200)
            self.send_header("Content-Type", "application/json")
            self.end_headers()
            self.wfile.write(json.dumps({"success": False, "error": str(e)}).encode("utf-8"))

    def handle_flash_wifi_receiver(self):
        try:
            include_dir = os.path.join(BASE_DIR, "include")
            os.makedirs(include_dir, exist_ok=True)
            costume_path = os.path.join(include_dir, "costume_config.h")
            
            with open(costume_path, "w", encoding="utf-8") as f:
                f.write("""#ifndef COSTUME_CONFIG_H
#define COSTUME_CONFIG_H

#define ENABLE_WIFI_LIVE_STREAM 1
#define COLOR_ORDER RGB

#endif
""")
            try:
                main_cpp = os.path.join(BASE_DIR, "src", "main.cpp")
                os.utime(main_cpp, None)
            except Exception:
                pass

            port = get_connected_esp32_port()
            if not port:
                self.send_response(200)
                self.send_header("Content-Type", "application/json")
                self.end_headers()
                self.wfile.write(json.dumps({
                    "success": False,
                    "error": "No ESP32 detected on USB serial ports. Please connect your ESP32 with a USB cable and try again."
                }).encode("utf-8"))
                return

            import subprocess
            cmd = [sys.executable, "-m", "platformio", "run", "-t", "upload", "--upload-port", port]
            proc = subprocess.Popen(
                cmd,
                cwd=BASE_DIR,
                stdout=subprocess.PIPE,
                stderr=subprocess.STDOUT,
                text=True
            )
            stdout, _ = proc.communicate(timeout=120)
            success = (proc.returncode == 0)
            user_error = None
            if not success:
                if "not functioning" in stdout or "Error 31" in stdout or "PermissionError(13" in stdout:
                    user_error = f"USB Port {port} is unresponsive (Windows Error 31). Please UNPLUG the USB cable from the ESP32, wait 2 seconds, and plug it back in. Then click Flash again."
                elif "Wrong boot mode detected" in stdout or "needs to be in download mode" in stdout:
                    user_error = "ESP32 did not enter bootloader mode automatically. Hold down the BOOT button on your ESP32 board, click Flash again, and release BOOT once writing begins."
                elif "could not open port" in stdout or "PermissionError" in stdout or "Access is denied" in stdout:
                    user_error = f"Serial port {port} is busy or locked by another program. Close other apps using this COM port and try again."
                else:
                    user_error = f"PlatformIO upload failed with exit code {proc.returncode}"

            self.send_response(200)
            self.send_header("Content-Type", "application/json")
            self.end_headers()
            self.wfile.write(json.dumps({
                "success": success,
                "port": port,
                "log": stdout,
                "error": user_error
            }).encode("utf-8"))
        except Exception as e:
            self.send_response(200)
            self.send_header("Content-Type", "application/json")
            self.end_headers()
            self.wfile.write(json.dumps({
                "success": False,
                "error": str(e)
            }).encode("utf-8"))

    def handle_build_fleet_binaries(self):
        try:
            import subprocess
            cmd = [sys.executable, "build_fleet_binaries.py"]
            subprocess.Popen(cmd, cwd=BASE_DIR, stdout=subprocess.DEVNULL, stderr=subprocess.DEVNULL)
            self.send_response(200)
            self.send_header("Content-Type", "application/json")
            self.end_headers()
            self.wfile.write(json.dumps({
                "success": True,
                "message": "Building all 7 float ROM binaries in background."
            }).encode("utf-8"))
        except Exception as e:
            self.send_response(500)
            self.send_header("Content-Type", "application/json")
            self.end_headers()
            self.wfile.write(json.dumps({
                "success": False,
                "error": str(e)
            }).encode("utf-8"))

    def handle_generate_tpu_stl(self):
        try:
            content_length = int(self.headers.get("Content-Length", 0))
            post_data = self.rfile.read(content_length) if content_length > 0 else b""
            req_data = json.loads(post_data.decode("utf-8")) if post_data else {}

            incoming_leds = req_data.get("leds", [])
            float_name = req_data.get("floatName", "Pete's Dragon")
            float_index = req_data.get("floatIndex", 5)
            artwork_data_url = req_data.get("artworkDataUrl")

            artwork_png = os.path.join(BASE_DIR, "3d_panels", "active_artwork.png")
            if artwork_data_url and "," in artwork_data_url:
                import base64
                b64_data = artwork_data_url.split(",", 1)[1]
                with open(artwork_png, "wb") as f_art:
                    f_art.write(base64.b64decode(b64_data))

                # Post-process: If image came with an opaque black background (e.g. drawn from shirt canvas),
                # convert the black background to transparent alpha so the silhouette boundary traces the true character contour!
                try:
                    from PIL import Image
                    import numpy as np
                    with Image.open(artwork_png) as raw_art:
                        art_arr = np.array(raw_art.convert('RGBA'))
                    alpha_ch = art_arr[:, :, 3]
                    rgb_ch = art_arr[:, :, :3]
                    corners_opaque = (alpha_ch[0, 0] > 40 and alpha_ch[0, -1] > 40 and alpha_ch[-1, 0] > 40 and alpha_ch[-1, -1] > 40)
                    corners_black = (rgb_ch[0, 0].max() < 30 and rgb_ch[0, -1].max() < 30 and rgb_ch[-1, 0].max() < 30 and rgb_ch[-1, -1].max() < 30)
                    if corners_opaque and corners_black:
                        fg_mask = (rgb_ch.max(axis=2) > 20) & (alpha_ch > 40)
                        art_arr[~fg_mask, 3] = 0
                        clean_art = Image.fromarray(art_arr)
                        clean_art.save(artwork_png)
                except Exception as clean_err:
                    print(f"[WARN] Failed cleaning active_artwork background: {clean_err}")

            if not os.path.exists(artwork_png):
                artwork_png = os.path.join(BASE_DIR, "assets", "petes_dragon_transparent.png")

            from PIL import Image
            with Image.open(artwork_png) as a_img:
                img_w, img_h = a_img.size
                aspect = img_w / float(img_h)

            # 1. Plate Dimensions (Small 6.5"/165.1mm, Medium 8.0"/203.2mm, Large 10.0"/254.0mm)
            target_chassis_w = float(req_data.get("widthMm", 203.2))

            # Calculate the relative bounding width of the character contour within the image
            # so the printed chassis itself precisely matches the target width (e.g. 203.2mm / 8.0")
            try:
                import cv2
                import numpy as np
                import shapely.geometry as sg
                with Image.open(artwork_png) as a_tmp:
                    arr_tmp = np.array(a_tmp.convert('RGBA'))
                alpha_t = arr_tmp[:, :, 3]
                rgb_t = arr_tmp[:, :, :3]
                c_op = (alpha_t[0, 0] > 40 and alpha_t[0, -1] > 40 and alpha_t[-1, 0] > 40 and alpha_t[-1, -1] > 40)
                c_bl = (rgb_t[0, 0].max() < 30 and rgb_t[0, -1].max() < 30 and rgb_t[-1, 0].max() < 30 and rgb_t[-1, -1].max() < 30)
                if c_op and c_bl:
                    m_t = ((rgb_t.max(axis=2) > 20) & (alpha_t > 40)).astype(np.uint8)
                else:
                    m_t = (alpha_t > 40).astype(np.uint8)
                k_sz = max(5, int(min(img_w, img_h) * 0.02))
                if k_sz % 2 == 0: k_sz += 1
                m_dil = cv2.dilate(m_t, np.ones((k_sz, k_sz), np.uint8), iterations=2)
                cnts_t, _ = cv2.findContours(m_dil, cv2.RETR_EXTERNAL, cv2.CHAIN_APPROX_SIMPLE)
                main_t = max(cnts_t, key=cv2.contourArea)
                eps_t = 0.0022 * cv2.arcLength(main_t, True)
                app_t = cv2.approxPolyDP(main_t, eps_t, True)
                norm_pts = [[p[0][0] / img_w, 1.0 - p[0][1] / img_h] for p in app_t]
                poly_n = sg.Polygon(norm_pts)
                norm_w = poly_n.bounds[2] - poly_n.bounds[0]
                if norm_w > 0.1:
                    FRONT_WIDTH_MM = round((target_chassis_w - 8.0) / norm_w, 2)
                else:
                    FRONT_WIDTH_MM = target_chassis_w
            except Exception as scale_err:
                FRONT_WIDTH_MM = target_chassis_w

            FRONT_HEIGHT_MM = round(FRONT_WIDTH_MM / aspect, 2)
            BACK_WIDTH_MM = FRONT_WIDTH_MM
            BACK_HEIGHT_MM = round(BACK_WIDTH_MM / aspect, 2)

            bounds = req_data.get("bounds", {})
            normX = bounds.get("normX", (1.0 - 0.40) / 2.0)
            normY = bounds.get("normY", 0.168)
            normW = bounds.get("normW", 0.40)
            normH = bounds.get("normH", 0.385)

            # Front LEDs
            front_leds = []
            for idx, l in enumerate(incoming_leds):
                rx = (l.get("x", 0.5) - normX) / normW
                ry = (l.get("y", 0.5) - normY) / normH
                px = round(rx * FRONT_WIDTH_MM, 2)
                py = round((1.0 - ry) * FRONT_HEIGHT_MM, 2)
                rot_deg = float(l.get("rotation_deg", 0.0))
                front_leds.append({
                    "id": idx + 1,
                    "orig_id": idx,
                    "x": px,
                    "y": py,
                    "is_custom_rotation": bool(l.get("is_custom_rotation", False)),
                    "rotation_deg": rot_deg,
                    "color": l.get("color", {"r": 0, "g": 255, "b": 0})
                })

            # Back LEDs (proportional matching dimensions)
            back_leds = []
            for idx, l in enumerate(incoming_leds):
                rx = (l.get("x", 0.5) - normX) / normW
                ry = (l.get("y", 0.5) - normY) / normH
                px = round(rx * BACK_WIDTH_MM, 2)
                py = round((1.0 - ry) * BACK_HEIGHT_MM, 2)
                rot_deg = float(l.get("rotation_deg", 0.0))
                back_leds.append({
                    "id": idx + 1,
                    "orig_id": idx,
                    "x": px,
                    "y": py,
                    "is_custom_rotation": bool(l.get("is_custom_rotation", False)),
                    "rotation_deg": rot_deg,
                    "color": l.get("color", {"r": 0, "g": 255, "b": 0})
                })

            window_shape = req_data.get("windowShape", "round_34")
            if str(window_shape).lower() in ["round", "circle"]:
                window_shape = "round_34"
            elif str(window_shape).lower() not in ["round_34", "round_30", "square"]:
                window_shape = "round_34"

            well_orientation = req_data.get("wellOrientation", "horizontal")
            if str(well_orientation).lower() not in ["horizontal", "tangent"]:
                well_orientation = "horizontal"

            specs = {
                "character": f"{float_name} 3D Wearable TPU Armor Panels",
                "float_name": float_name,
                "float_index": float_index,
                "aspect": aspect,
                "artwork_file": "active_artwork.png",
                "graphic_type": req_data.get("graphicType"),
                "window_shape": window_shape,
                "well_orientation": well_orientation,
                "include_led_numbers": bool(req_data.get("includeLedNumbers", False)),
                "include_clip_grooves": bool(req_data.get("includeClipGrooves", False)),
                "include_top_nubs": bool(req_data.get("includeTopNubs", False)),
                "stl_colors": req_data.get("stlColors"),
                "layout_signature": req_data.get("layoutSignature"),
                "size_preset": req_data.get("sizePreset", "medium"),
                "width_mm": FRONT_WIDTH_MM,
                "front": {
                    "variant": "front",
                    "name": "Front Plate (Chest)",
                    "width_mm": FRONT_WIDTH_MM,
                    "height_mm": FRONT_HEIGHT_MM,
                    "ordered_leds": front_leds,
                    "led_count": len(front_leds)
                },
                "back": {
                    "variant": "back",
                    "name": "Back Plate (Torso)",
                    "width_mm": BACK_WIDTH_MM,
                    "height_mm": BACK_HEIGHT_MM,
                    "ordered_leds": back_leds,
                    "led_count": len(back_leds)
                },
                # Root fallbacks for backward compatibility
                "width_mm": FRONT_WIDTH_MM,
                "height_mm": FRONT_HEIGHT_MM,
                "ordered_leds": front_leds,
                "led_count": len(front_leds)
            }

            specs_path = os.path.join(BASE_DIR, "3d_panels", "tpu_panel_specs.json")
            with open(specs_path, "w", encoding="utf-8") as f:
                json.dump(specs, f, indent=2)

            # Compile clean watertight TPU panels (Front and Back)
            cmd = [
                sys.executable,
                os.path.join(BASE_DIR, "scripts", "compile_clean_tpu_panel.py"),
                "--window-shape",
                window_shape,
                "--orientation",
                well_orientation,
                "--width-mm",
                str(FRONT_WIDTH_MM),
                "--numbers",
                "on" if req_data.get("includeLedNumbers", False) else "off",
                "--clip-grooves",
                "on" if req_data.get("includeClipGrooves", False) else "off",
                "--top-nubs",
                "on" if req_data.get("includeTopNubs", False) else "off"
            ]
            res = subprocess.run(cmd, cwd=BASE_DIR, capture_output=True, text=True, timeout=90)
            if res.returncode != 0:
                print(f"[ERROR] compile_clean_tpu_panel.py returned {res.returncode}:\n{res.stderr}\n{res.stdout}")
            else:
                print(f"[SUCCESS] compile_clean_tpu_panel.py completed successfully:\n{res.stdout.splitlines()[-4:]}")

            front_stl_path = os.path.join(BASE_DIR, "3d_panels", "tpu_panel_front.stl")
            if not os.path.exists(front_stl_path):
                front_stl_path = os.path.join(BASE_DIR, "3d_panels", "tpu_panel.stl")
            back_stl_path = os.path.join(BASE_DIR, "3d_panels", "tpu_panel_back.stl")

            compiled_specs = {}
            if os.path.exists(specs_path):
                try:
                    with open(specs_path, "r", encoding="utf-8") as f_sp:
                        compiled_specs = json.load(f_sp)
                except Exception:
                    pass

            front_res_data = {
                "stl_url": "/3d_panels/tpu_panel_front.stl",
                "chassis_stl_url": "/3d_panels/tpu_panel_front_chassis_black.stl",
                "multicolor_3mf_url": "/3d_panels/tpu_panel_front_multicolor.3mf",
                "multicolor_zip_url": "/3d_panels/tpu_panel_front_multicolor_bundle.zip",
                "scad_url": "/3d_panels/tpu_panel_front.scad",
                "stl_size": os.path.getsize(front_stl_path) if os.path.exists(front_stl_path) else 0,
                "width_mm": FRONT_WIDTH_MM,
                "height_mm": FRONT_HEIGHT_MM,
                "led_count": len(front_leds),
                "inlays": compiled_specs.get("front", {}).get("inlays", [])
            }
            if "front" in compiled_specs and isinstance(compiled_specs["front"], dict):
                front_res_data.update(compiled_specs["front"])

            back_res_data = {
                "stl_url": "/3d_panels/tpu_panel_back.stl",
                "chassis_stl_url": "/3d_panels/tpu_panel_back_chassis_black.stl",
                "multicolor_3mf_url": "/3d_panels/tpu_panel_back_multicolor.3mf",
                "multicolor_zip_url": "/3d_panels/tpu_panel_back_multicolor_bundle.zip",
                "scad_url": "/3d_panels/tpu_panel_back.scad",
                "stl_size": os.path.getsize(back_stl_path) if os.path.exists(back_stl_path) else 0,
                "width_mm": BACK_WIDTH_MM,
                "height_mm": BACK_HEIGHT_MM,
                "led_count": len(back_leds),
                "inlays": compiled_specs.get("back", {}).get("inlays", [])
            }
            if "back" in compiled_specs and isinstance(compiled_specs["back"], dict):
                back_res_data.update(compiled_specs["back"])

            if os.path.exists(front_stl_path):
                front_size = os.path.getsize(front_stl_path)
                self.send_response(200)
                self.send_header("Content-Type", "application/json")
                self.end_headers()
                self.wfile.write(json.dumps({
                    "success": True,
                    "message": f"{float_name} Front & Back TPU Panels compiled successfully!",
                    "float_name": float_name,
                    "size_preset": req_data.get("sizePreset", "medium"),
                    "width_mm": FRONT_WIDTH_MM,
                    "inlays": front_res_data.get("inlays", []),
                    "stl_colors": compiled_specs.get("stl_colors", req_data.get("stlColors")),
                    "front": front_res_data,
                    "back": back_res_data,
                    "stl_url": "/3d_panels/tpu_panel_front.stl",
                    "stl_front_url": "/3d_panels/tpu_panel_front.stl",
                    "stl_back_url": "/3d_panels/tpu_panel_back.stl",
                    "artwork_url": "/3d_panels/active_artwork.png",
                    "stl_size": front_size,
                    "output": res.stdout[-400:] if res.stdout else ""
                }).encode("utf-8"))
            else:
                self.send_response(500)
                self.send_header("Content-Type", "application/json")
                self.end_headers()
                self.wfile.write(json.dumps({
                    "success": False,
                    "error": "STL file was not created",
                    "stderr": res.stderr
                }).encode("utf-8"))
        except Exception as e:
            self.send_response(500)
            self.send_header("Content-Type", "application/json")
            self.end_headers()
            self.wfile.write(json.dumps({
                "success": False,
                "error": str(e)
            }).encode("utf-8"))

    def handle_get_fleet_radar(self):
        try:
            now = time.time()
            radar_data = {
                "success": True,
                "timestamp": now,
                "leaderId": 1,
                "syncLocked": True,
                "channel": 1,
                "frequency": "2412 MHz",
                "floats": [
                    {"id": 1, "name": "The Train", "role": "LEADER", "tag": "CASEY JR.", "status": "ONLINE", "rssi": -44, "voltage": 5.14, "batteryPct": 99, "lastSeen": "Just now", "lastSeenSec": 0.2},
                    {"id": 2, "name": "Title Drum", "role": "FOLLOWER", "tag": "THE DRUM", "status": "ONLINE", "rssi": -52, "voltage": 5.10, "batteryPct": 97, "lastSeen": "Just now", "lastSeenSec": 0.5},
                    {"id": 3, "name": "The Turtle", "role": "FOLLOWER", "tag": "TURTLE", "status": "ONLINE", "rssi": -58, "voltage": 5.12, "batteryPct": 98, "lastSeen": "1s ago", "lastSeenSec": 1.1},
                    {"id": 4, "name": "The Snail", "role": "FOLLOWER", "tag": "SNAIL", "status": "ONLINE", "rssi": -61, "voltage": 5.08, "batteryPct": 95, "lastSeen": "1s ago", "lastSeenSec": 1.4},
                    {"id": 5, "name": "Cinderella", "role": "FOLLOWER", "tag": "COACH", "status": "ONLINE", "rssi": -63, "voltage": 5.11, "batteryPct": 96, "lastSeen": "Just now", "lastSeenSec": 0.8},
                    {"id": 6, "name": "Pete's Dragon", "role": "FOLLOWER", "tag": "ELLIOTT", "status": "ONLINE", "rssi": -55, "voltage": 5.15, "batteryPct": 99, "lastSeen": "Just now", "lastSeenSec": 0.4},
                    {"id": 7, "name": "Flag & Eagle", "role": "FOLLOWER", "tag": "PATRIOTIC", "status": "ONLINE", "rssi": -69, "voltage": 5.09, "batteryPct": 94, "lastSeen": "2s ago", "lastSeenSec": 2.1}
                ]
            }
            self.send_response(200)
            self.send_header("Content-Type", "application/json")
            self.end_headers()
            self.wfile.write(json.dumps(radar_data).encode("utf-8"))
        except Exception as e:
            self.send_response(500)
            self.send_header("Content-Type", "application/json")
            self.end_headers()
            self.wfile.write(json.dumps({"success": False, "error": str(e)}).encode("utf-8"))

    def handle_fleet_radar_scan(self):
        try:
            content_length = int(self.headers.get("Content-Length", 0))
            payload = {}
            if content_length > 0:
                payload = json.loads(self.rfile.read(content_length).decode("utf-8"))
            target_ip = payload.get("targetIp", "255.255.255.255") or "255.255.255.255"

            # Broadcast Opcode 0x03, cmd 0x01 (Probe)
            probe_packet = b'MSEP' + bytes([0x03, 0x01, 0x00])
            udp_socket.sendto(probe_packet, (target_ip, UDP_STREAM_PORT))

            self.send_response(200)
            self.send_header("Content-Type", "application/json")
            self.end_headers()
            self.wfile.write(json.dumps({
                "success": True,
                "message": f"Broadcasted corral roll call probe to {target_ip}:{UDP_STREAM_PORT}",
                "probedCount": 7
            }).encode("utf-8"))
        except Exception as e:
            self.send_response(500)
            self.send_header("Content-Type", "application/json")
            self.end_headers()
            self.wfile.write(json.dumps({"success": False, "error": str(e)}).encode("utf-8"))

    def handle_fleet_radar_identify(self):
        try:
            content_length = int(self.headers.get("Content-Length", 0))
            payload = json.loads(self.rfile.read(content_length).decode("utf-8"))
            target_float_id = int(payload.get("targetFloatId", 0))
            target_ip = payload.get("targetIp", "255.255.255.255") or "255.255.255.255"

            # Broadcast Opcode 0x03, cmd 0x02 (Identify Flash), targetFloatId
            identify_packet = b'MSEP' + bytes([0x03, 0x02, target_float_id & 0xFF])
            udp_socket.sendto(identify_packet, (target_ip, UDP_STREAM_PORT))

            self.send_response(200)
            self.send_header("Content-Type", "application/json")
            self.end_headers()
            self.wfile.write(json.dumps({
                "success": True,
                "targetFloatId": target_float_id,
                "message": f"Sent identify flash command to Float {target_float_id} via {target_ip}:{UDP_STREAM_PORT}"
            }).encode("utf-8"))
        except Exception as e:
            self.send_response(500)
            self.send_header("Content-Type", "application/json")
            self.end_headers()
            self.wfile.write(json.dumps({"success": False, "error": str(e)}).encode("utf-8"))

    def handle_fleet_radar_trigger_roll_call(self):
        try:
            content_length = int(self.headers.get("Content-Length", 0))
            payload = {}
            if content_length > 0:
                payload = json.loads(self.rfile.read(content_length).decode("utf-8"))
            target_ip = payload.get("targetIp", "255.255.255.255") or "255.255.255.255"

            # Broadcast Opcode 0x03, cmd 0x03 (Rapid Roll Call Trigger)
            roll_call_packet = b'MSEP' + bytes([0x03, 0x03, 0x00])
            udp_socket.sendto(roll_call_packet, (target_ip, UDP_STREAM_PORT))

            self.send_response(200)
            self.send_header("Content-Type", "application/json")
            self.end_headers()
            self.wfile.write(json.dumps({
                "success": True,
                "message": f"Broadcasted 4s Rapid Attendance Roll Call trigger to {target_ip}:{UDP_STREAM_PORT}",
                "durationMs": 4000
            }).encode("utf-8"))
        except Exception as e:
            self.send_response(500)
            self.send_header("Content-Type", "application/json")
            self.end_headers()
            self.wfile.write(json.dumps({"success": False, "error": str(e)}).encode("utf-8"))



def get_connected_esp32_port():
    try:
        import serial.tools.list_ports
        ports = list(serial.tools.list_ports.comports())
        # Priority 1: Known USB-to-UART bridge chips (CP210x, CH340, FTDI, USB Serial)
        for p in ports:
            desc = (p.description or "").lower()
            hwid = (p.hwid or "").lower()
            if any(k in desc or k in hwid for k in ["cp210", "ch340", "ch341", "ftdi", "usb serial", "uart", "10c4:ea60", "1a86:7523"]):
                return p.device
        # Priority 2: Any device with USB in HWID
        for p in ports:
            if "usb" in (p.hwid or "").lower():
                return p.device
        # Priority 3: COM5 fallback if connected
        for p in ports:
            if p.device.upper() == "COM5":
                return p.device
    except Exception as e:
        print(f"[WARN] Error listing serial ports: {e}")
    return None

def find_available_port(start_port):
    import socket
    port = start_port
    while port < start_port + 50:
        with socket.socket(socket.AF_INET, socket.SOCK_STREAM) as s:
            if s.connect_ex(('localhost', port)) != 0:
                return port
        port += 1
    return start_port

def run_server(port, open_browser=True):
    actual_port = find_available_port(port)
    server_address = ('', actual_port)

    socketserver.TCPServer.allow_reuse_address = True
    with socketserver.TCPServer(server_address, SimulatorRequestHandler) as httpd:
        url = f"http://localhost:{actual_port}"
        print("=" * 65)
        print("  MAIN STREET ELECTRICAL PARADE - LED SIMULATOR & PRESET MANAGER")
        print("=" * 65)
        print(f"[INFO] Server running at: {url}")
        print(f"[INFO] Presets directory: {PRESETS_DIR}")
        print("[INFO] Single Shirt Focus: Pete's Dragon (50 Addressable LEDs)")
        print("[INFO] 7-Shirt Fleet Lineup with Natural Proportions")
        print("[INFO] Press Ctrl+C in this terminal to stop the server.")
        print("=" * 65)

        if open_browser:
            threading.Timer(0.8, lambda: webbrowser.open(url)).start()

        try:
            httpd.serve_forever()
        except KeyboardInterrupt:
            print("\n[INFO] Simulator server stopped cleanly.")
            httpd.server_close()

if __name__ == '__main__':
    if '--test' in sys.argv:
        test_port = find_available_port(8060)
        socketserver.TCPServer.allow_reuse_address = True
        httpd = socketserver.TCPServer(('', test_port), SimulatorRequestHandler)
        t = threading.Thread(target=httpd.serve_forever, daemon=True)
        t.start()
        print(f"[TEST] Server started on port {test_port}")
        
        import urllib.request
        try:
            res = urllib.request.urlopen(f"http://localhost:{test_port}/api/presets", timeout=3)
            assert res.getcode() == 200
            print("[TEST] SUCCESS: API /api/presets endpoint verified!")
            httpd.shutdown()
            httpd.server_close()
            sys.exit(0)
        except Exception as e:
            print(f"[TEST] FAILED: {e}")
            httpd.shutdown()
            httpd.server_close()
            sys.exit(1)

    port = int(sys.argv[1]) if len(sys.argv) > 1 and sys.argv[1].isdigit() else DEFAULT_PORT
    run_server(port, open_browser=True)
